telzo2000/cool838chax/img/img00001.jpg

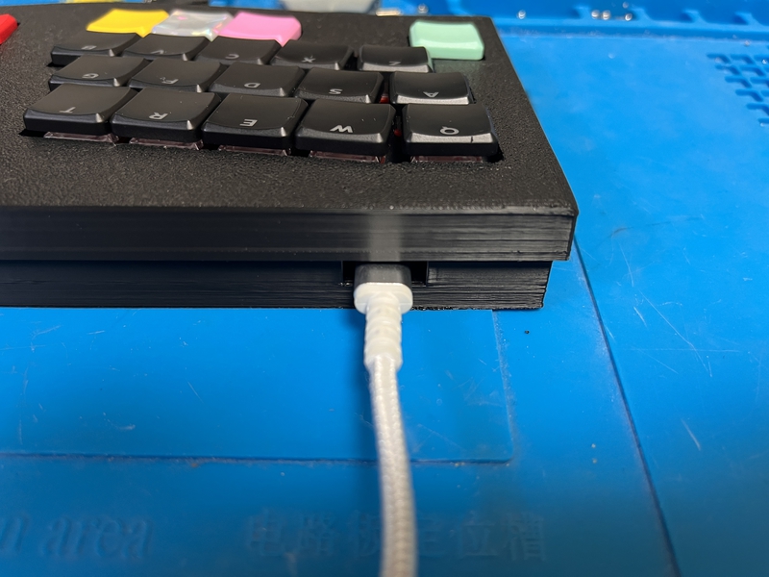
img/img00001.jpg
