telzo2000/cool838chax/img/img00003.jpg

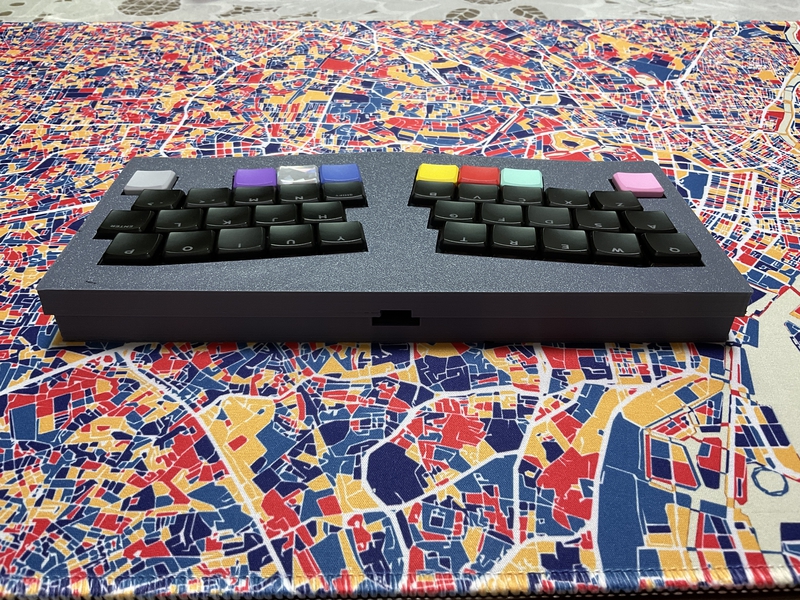
img/img00003.jpg
