telzo2000/cool838chax/img/img00004.jpg

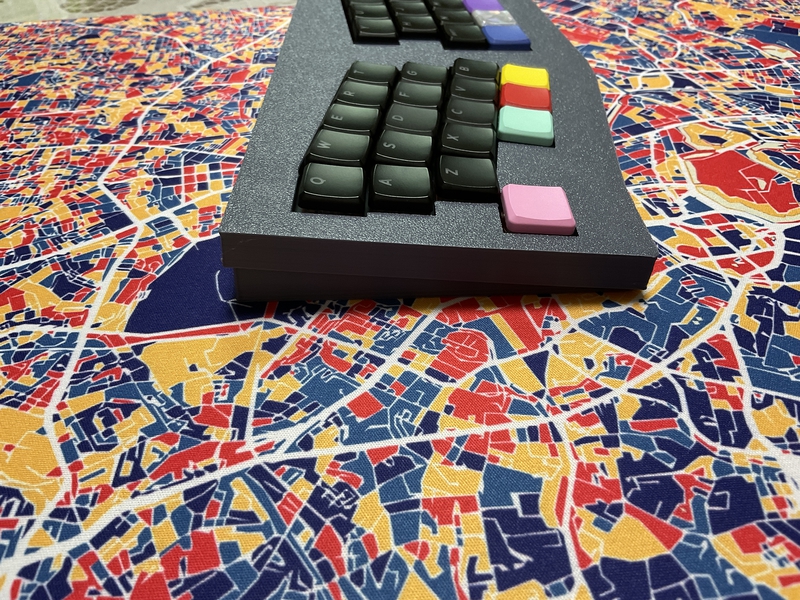
img/img00004.jpg
