telzo2000/cool838chax/img/img00006.jpg

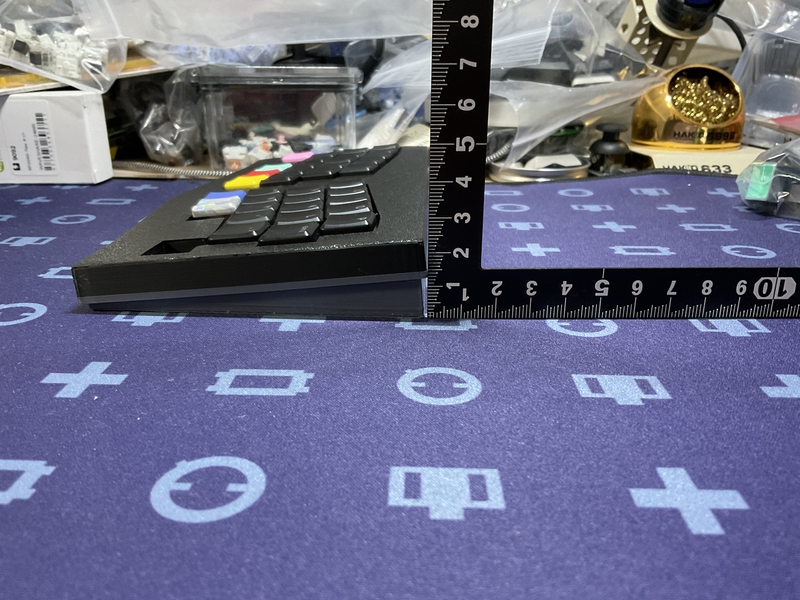
img/img00006.jpg
