telzo2000/cool838chax/img/img00007.jpg

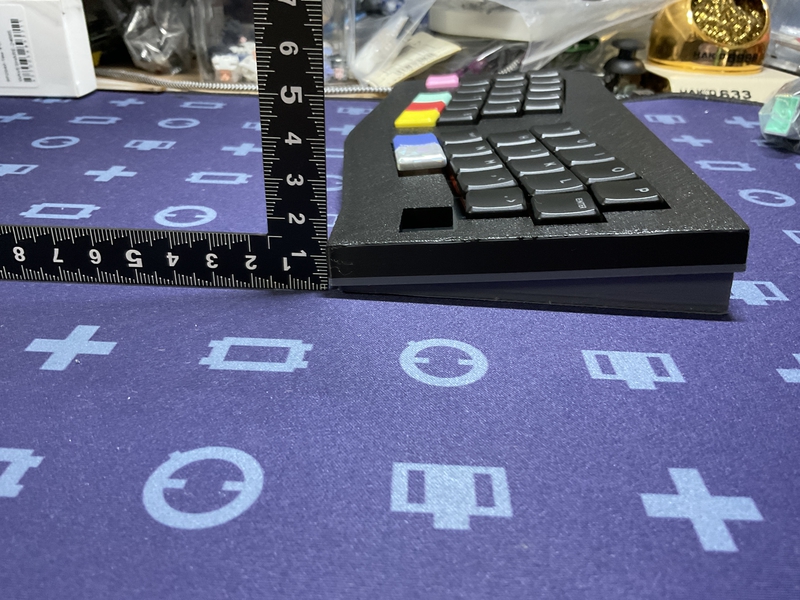
img/img00007.jpg
