telzo2000/cool838chax/img/img00008.jpg

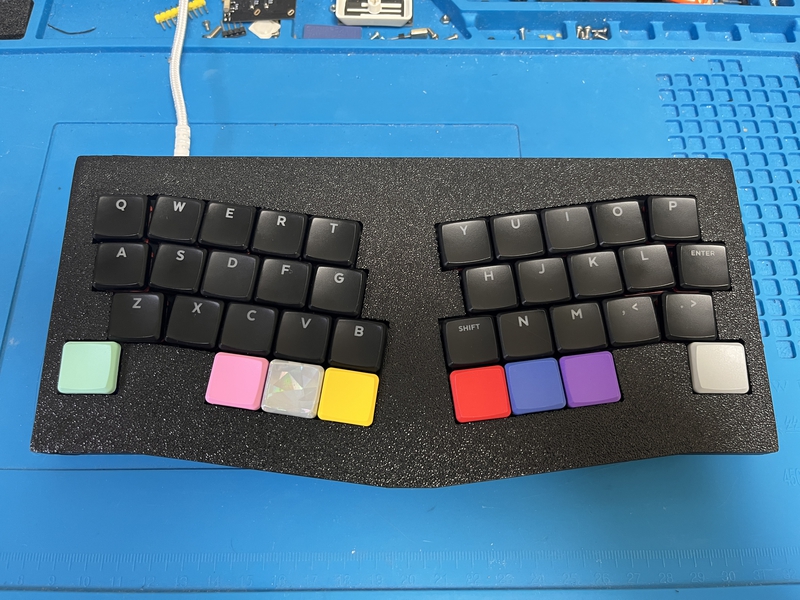
img/img00008.jpg
