telzo2000/cool838chax/img/img00010.jpg

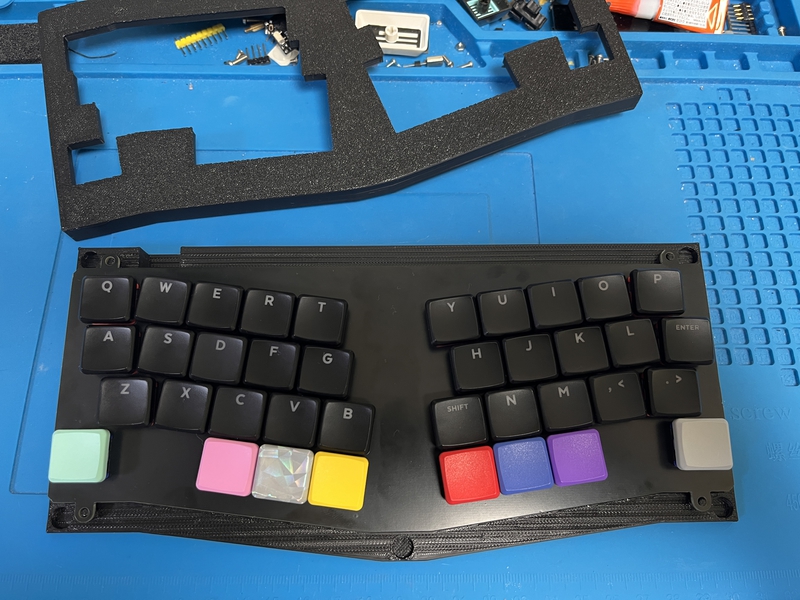
img/img00010.jpg
